yepher/eta-2824-2-watch/output/EXPORTS-2026-09-07.md

# Exports — 2026-09-07

Generated from `watch.cade --part watch` at revision *automatic framework
rebuilt as a stepped stack* (`ERRORS.md` E20, E21).

**The model has grown since the tables in `README.md` were measured**: it is now
**83 part definitions placed 103 times**, against the 71 and 94 those tables
were taken on. Nothing above is withdrawn — it was true of that revision — but
two of its conclusions do not survive the change, and both are re-measured
below. *A measurement has a date on it.*

| file | what it is | size |
|---|---|---|
| `watch.3mf` | the whole assembly, meshed | 141 MB |
| `watch.html` | one self-contained interactive page | 54 MB |
| `watch-raymarch.html` | the same 103 placements, no mesh | 1.6 MB |
| `watch_assembly.step` | **one file**: 43 parts, 54 placements, product tree | 2.2 MB |
| `step/` | the same parts one file each, **43** of them | 2.3 MB |

## Before committing any of this

`watch.3mf` is **141 MB and GitHub rejects a file over 100 MB** — not a warning,
a refused push. `watch.html` at 54 MB is over the 50 MB warning threshold but
goes through. The two options for the 3MF are Git LFS or a Release attachment,
and `README.md` above already recommends the second. The other three files are
small enough to commit normally.

## 3MF

`cade build watch.cade -o watch.3mf --part watch` — **no cell flag**, which is
the change from the README's recipe.

**`--cell 0.095mm` no longer passes.** Re-run today it fails on
`eta_pos_11_third_wheel_envelope` (2 pinched edges), and on the way there
`seconds_hand_envelope` meshes to **0 triangles** — the hands are finer than
that cell. Two more were tried, and the refusals name different parts each time:

| setting | what refuses |
|---|---|
| `--cell 0.1mm` | `eta_pos_16_barrel_bridge_envelope`, 68 pinched edges |
| `--cell 0.15mm` | `seconds_hand_envelope`, **0 triangles** |
| `--cell 0.095mm` | `eta_pos_11_third_wheel_envelope`, 2 pinched edges |
| `-n 64`, `-n 96`, `--cell 0.3mm` | `eta_pos_4_winding_stem_envelope`, 2 closed shells |

So the cell-size search the README describes has run out of answers on this
revision, and the reason is structural rather than bad luck: **the model spans
0.04 mm (hairspring wire) to 32 mm (case), and no single cell holds both.** The
default — each definition meshed on its own grid — is what per-definition grids
exist for, and it is the only setting that writes a valid file here.

**16 763 598 triangles, 8 381 766 vertices, 83 objects, 103 build items**, read
back and confirmed by **lib3mf 2.5.0**, the 3MF Consortium's own reader, which
agrees with cade on every one of those numbers. 1.32 GB as cade writes it
(entries stored); the file here is that archive deflated, which is the README's
own recipe and is legal 3MF — lib3mf and `trimesh` both return identical
geometry from it.

## STEP

`cade export --part watch` still refuses, and now names **41 of 83**:

| definition | faces with no confirmed loop set (n = 128) |
|---|---|
| `eta_pos_10_centre_seconds_wheel_envelope` | 322 of 325 |
| `eta_pos_25_automatic_framework_envelope` | 270 of 287 |
| `eta_pos_12_second_wheel_envelope` | 228 of 231 |
| `eta_pos_19_crown_wheel_envelope` | 158 of 188 |
| `eta_pos_14_barrel_envelope` | 151 of 159 |

No subassembly closes either — `case_and_hands_preview` refuses 6 of 9,
`main_plate_preview` 2 of 5. `step/` holds the **43** that do write. Forty write at `-n 128`; three needed a
raised division count, which is the README's own finding reproducing on a
different revision — and one of the three is the same part it names:

| part | needs |
|---|---|
| `hour_hand_envelope` | `-n 192` — **the README's number, independently** |
| `eta_pos_30_automatic_lower_bridge_envelope` | `-n 192` |
| `eta_pos_14_barrel_envelope` | `-n 256` |

Ten more were swept at 192 and 256 and recovered nothing, so the remaining 38
refuse on their own geometry rather than on resolution, exactly as the README
says of its own 30. `tools/build_step_assembly.py` composes them into
one placed AP214 file exactly as `README.md` describes.

### One file: `watch_assembly.step`

Written by **cade's own assembly writer**, not by an external composer — 43
definitions placed 54 times, with the AP214 product tree, the part names and the
colours, 2.2 MB, at `-n 256`.

The way round the whole-or-nothing rule is not to weaken it. That rule is about
a file that *silently* drops parts, and what it forbids is worth keeping. So
`../watch_exact.cade` is a generated Cade source that **states** which
definitions it contains and where each one sits — every placement is the world
frame `tools/cadeval.py` flattens out of the model — and what cade writes from
it is a *complete* export of a stated selection rather than a truncated export
of the watch. The file lists the 45 definitions left out, by name, in its own
header. Regenerate it with `tools/make_step_assembly.py`; the selection is read
from `step/`, so the two artefacts cannot disagree about what exports.

**Gate.** `cade export`'s own check re-imports the file and runs `verify`, and
it is structurally blind to the product tree, because
`NEXT_ASSEMBLY_USAGE_OCCURRENCE` appears nowhere in cade's importer — a file
whose placements were all wrong would pass it. Read back with **OpenCASCADE
7.9** (`tools/occt-assembly.py` in the cade tree): **54 occurrences, 43 of 43
solids valid, 0 invalid**, each at its located bounding box — the four train
jewels on their own pivots, the crystal at z −2.5 to −1.5, the crown at x 20,
the barrel at 99.995 mm³.

**Why `-n 256` and not the default.** An assembly export runs one `-n` for every
definition in it, and three of the 43 need a raised count of their own — the
barrel (256), the automatic lower bridge and the hour hand (192). At `-n 128`
the file writes in 45 seconds with 40 parts and those three refused; at 256 it
takes about eight minutes and takes all 43. The refusal names them either way,
so there is no silent version of this choice.

### A faceted whole-assembly STEP is now possible and is still not the answer

`cade export --part <assembly> --faceted` was **accepted and silently ignored**
until today — `export` matched the assembly branch before it looked at the flag
— and that is fixed upstream, with a test that fails against the old behaviour.
It does not rescue this model. A faceted `ADVANCED_FACE` costs **503 bytes per
triangle**, measured, so 16.8 M of them is **8.4 GB**, against 141 MB for the
same triangles as a deflated 3MF; and every coarser grid that would shrink it
breaks a part, per the table above. For a mesh of the whole watch, the 3MF is
the format.

## Interactive

- **`watch.html`** — drag to orbit, wheel to zoom, shift-drag to pan, the cube
  snaps to an axis, **hover a row to light that part, click to hide it**, and a
  slider explodes the assembly. Hide the case, caseback and crystal and the
  movement is underneath. Meshed at `-n 48`; `-n 64` and `-n 128` are the same
  command and give 95 MB and 381 MB.
- **`watch-raymarch.html`** — 1.6 MB for the same 103 placements, because the
  page raymarches cade's field per pixel rather than carrying a mesh. Needs
  WebGPU. It has **not** been confirmed rendering: the container it was built in
  loses the WebGPU device on a shader that size, which is a fact about that
  software rasteriser and not about the page, but unverified is unverified.

## Reproducing

```sh
cade build  watch.cade -o watch.3mf  --part watch
cade view   watch.cade -o watch.html --part watch -n 48
cade view   watch.cade -o watch-raymarch.html --part watch --raymarch
cade export eta_2824_design/<module>.cade -o step/<part>.step --part <part> -n 128
```
