yepher/eta-2824-2-watch/rendered/dial.png

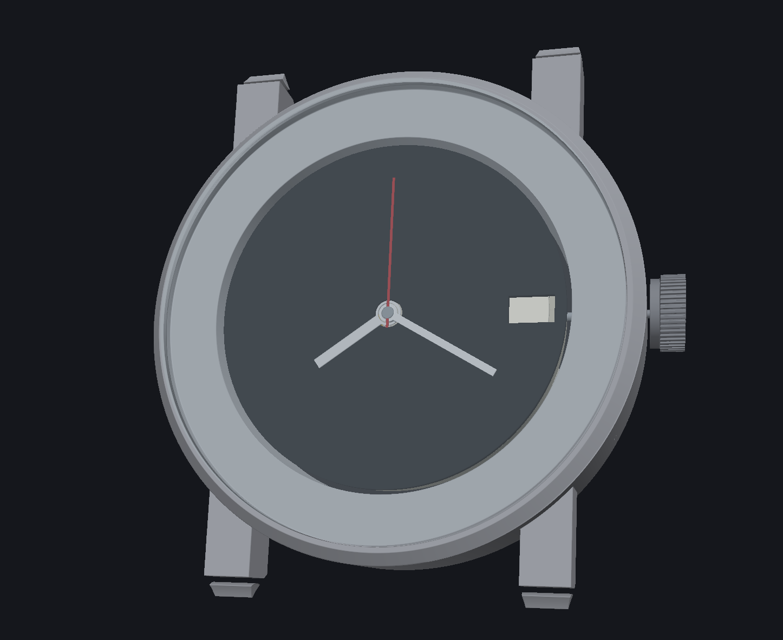
rendered/dial.png
