yepher/eta-2824-2-watch/rendered/exploded_view_editor.png

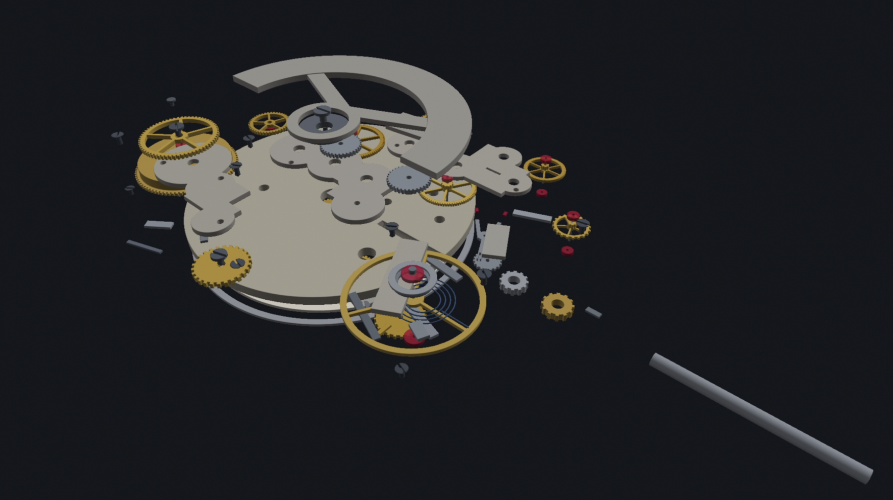
rendered/exploded_view_editor.png
