yepher/eta-2824-2-watch/rendered/thumbs/watch_render_hero.jpg

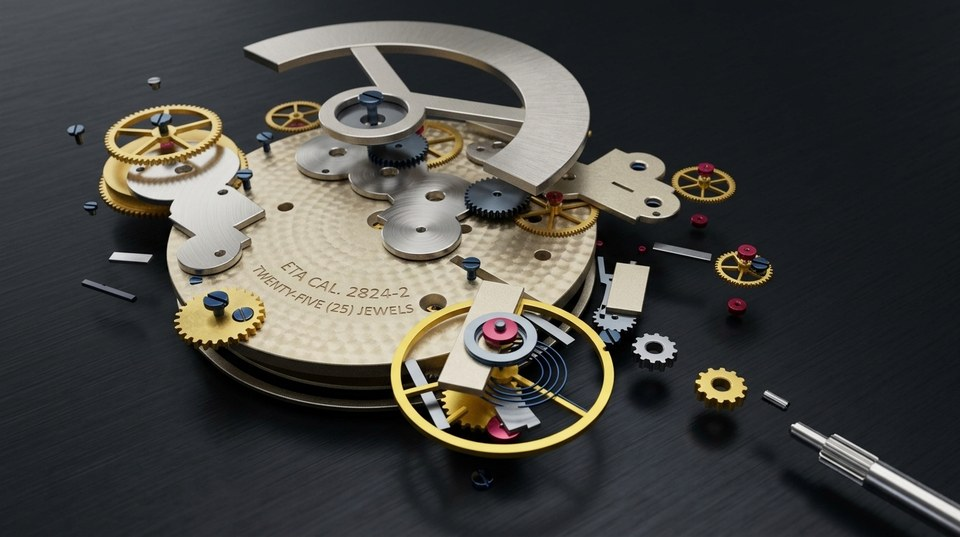
rendered/thumbs/watch_render_hero.jpg
