yepher/eta-2824-2-watch/output/step/eta_pos_7_yoke_envelope.step

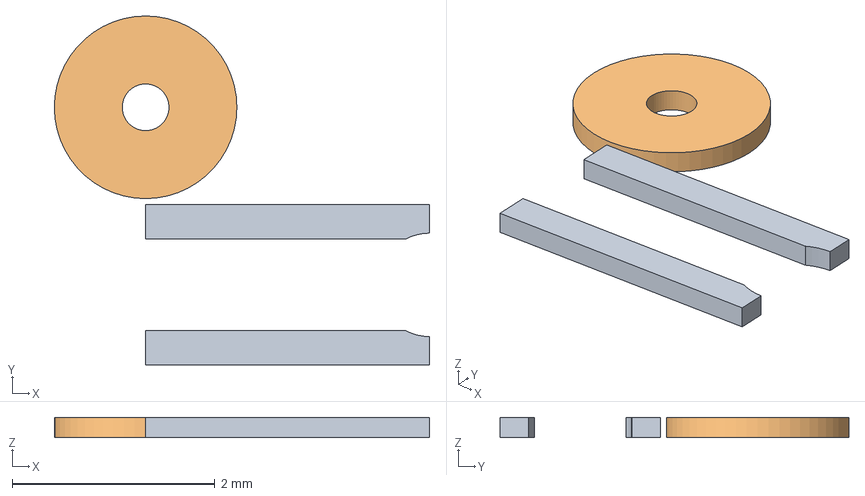
[picture p30: CAD file, 2026-09-07]
output/step/eta_pos_7_yoke_envelope.step
3.70 x 3.44 x 0.2 mm
