yepher/eta-2824-2-watch/output/step/eta_pos_31_3_rotor_pinion.step

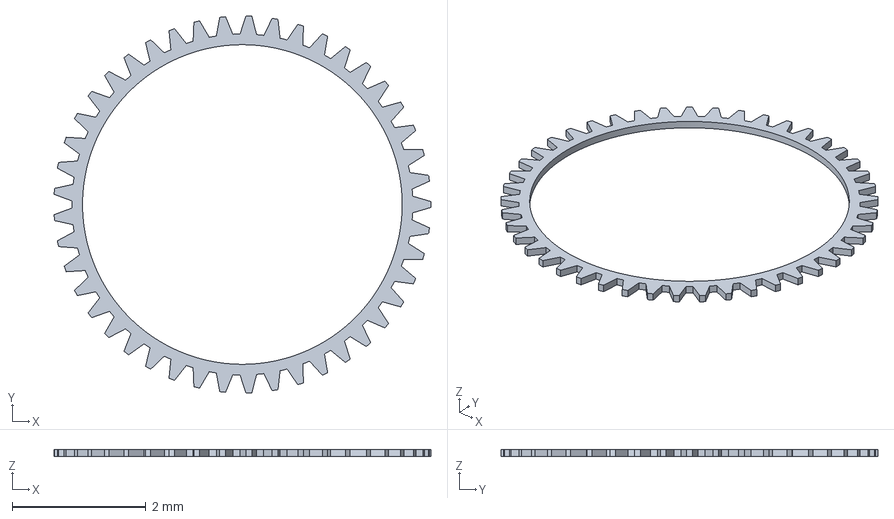
[picture p31: CAD file, 2026-09-07]
output/step/eta_pos_31_3_rotor_pinion.step
5.64 x 5.64 x 0.11 mm
