yepher/eta-2824-2-watch/output/step/eta_pos_23_impulse_jewel.step

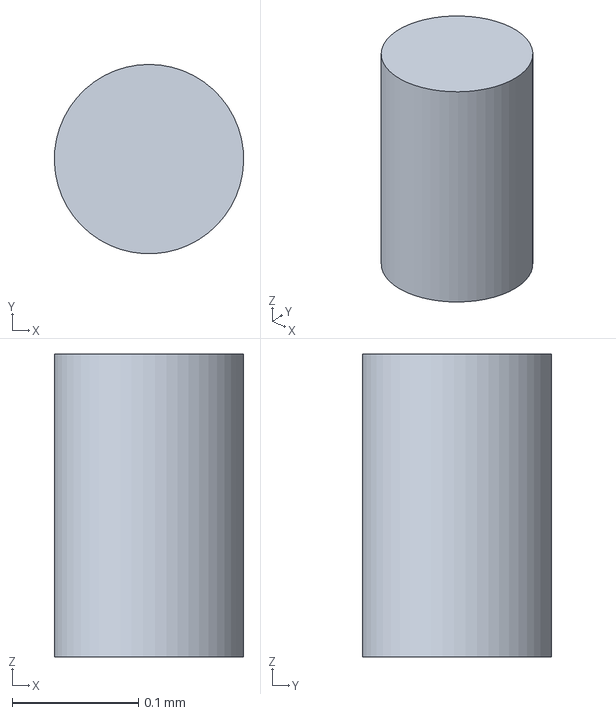
[picture p32: CAD file, 2026-09-07]
output/step/eta_pos_23_impulse_jewel.step
0.15 x 0.15 x 0.24 mm
