yepher/eta-2824-2-watch/output/step/eta_pos_23_balance_staff.step

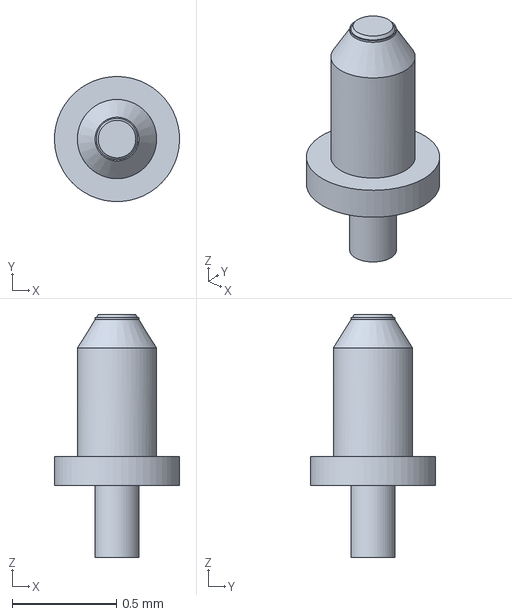
[picture p33: CAD file, 2026-09-07]
output/step/eta_pos_23_balance_staff.step
0.6 x 0.599 x 1.17 mm
