yepher/eta-2824-2-watch/output/step/eta_pos_6_setting_lever_envelope.step

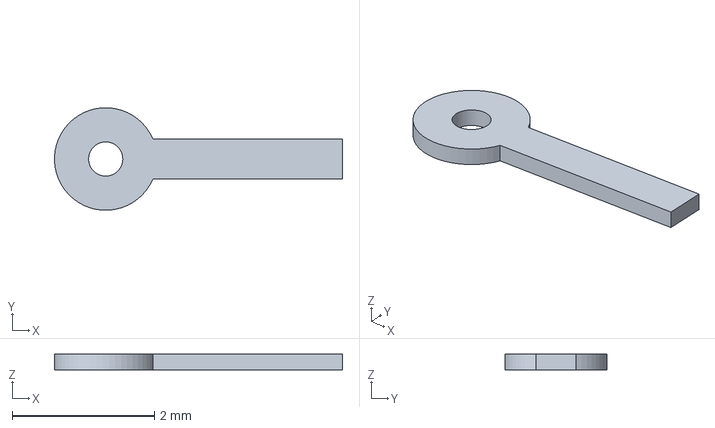
[picture p34: CAD file, 2026-09-07]
output/step/eta_pos_6_setting_lever_envelope.step
4.04 x 1.44 x 0.22 mm
