yepher/eta-2824-2-watch/output/step/click_post.step

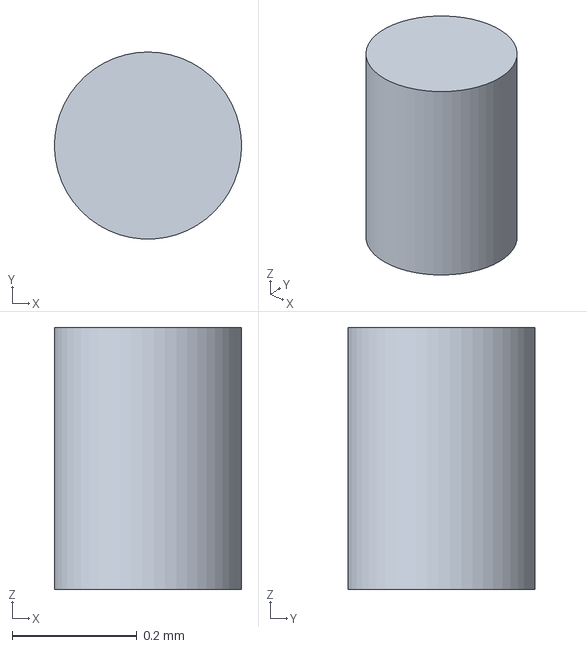
[picture p35: CAD file, 2026-09-07]
output/step/click_post.step
0.3 x 0.3 x 0.42 mm
