yepher/eta-2824-2-watch/output/step/eta_pos_33_cannon_pinion_envelope.step

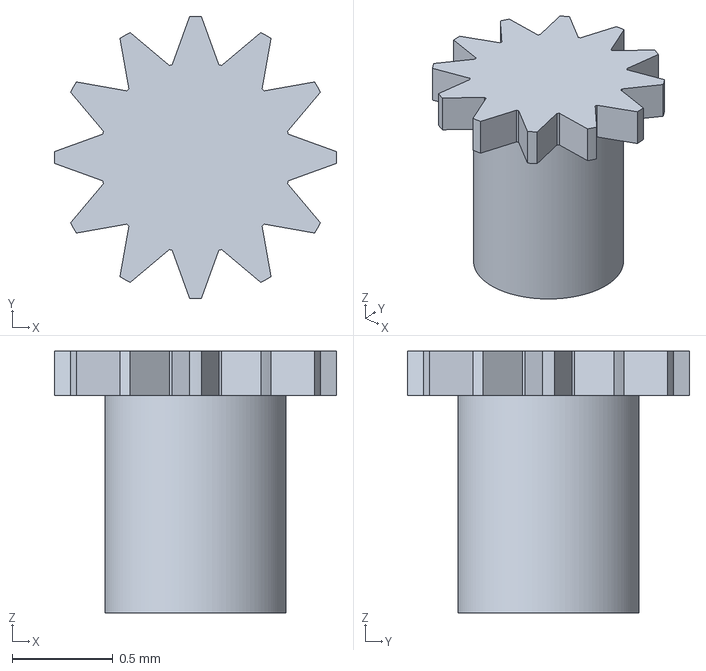
[picture p36: CAD file, 2026-09-07]
output/step/eta_pos_33_cannon_pinion_envelope.step
1.40 x 1.40 x 1.30 mm
