yepher/eta-2824-2-watch/output/step/eta_pos_14_barrel_envelope.step

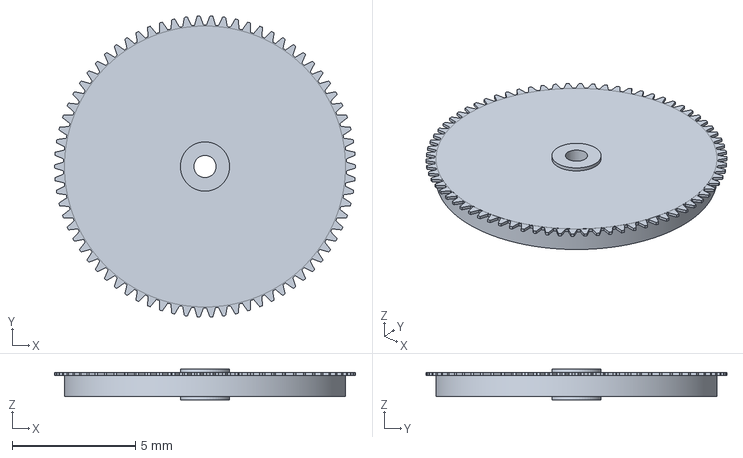
[picture p37: CAD file, 2026-09-07]
output/step/eta_pos_14_barrel_envelope.step
12.2 x 12.2 x 1.25 mm
