yepher/eta-2824-2-watch/output/step/eta_pos_17_click_envelope.step

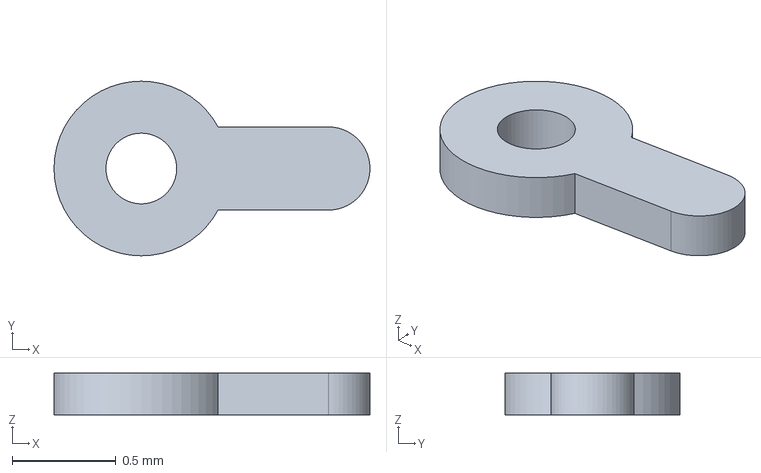
[picture p38: CAD file, 2026-09-07]
output/step/eta_pos_17_click_envelope.step
1.52 x 0.84 x 0.2 mm
