yepher/eta-2824-2-watch/output/step/eta_pos_13_train_bridge_jewel.step

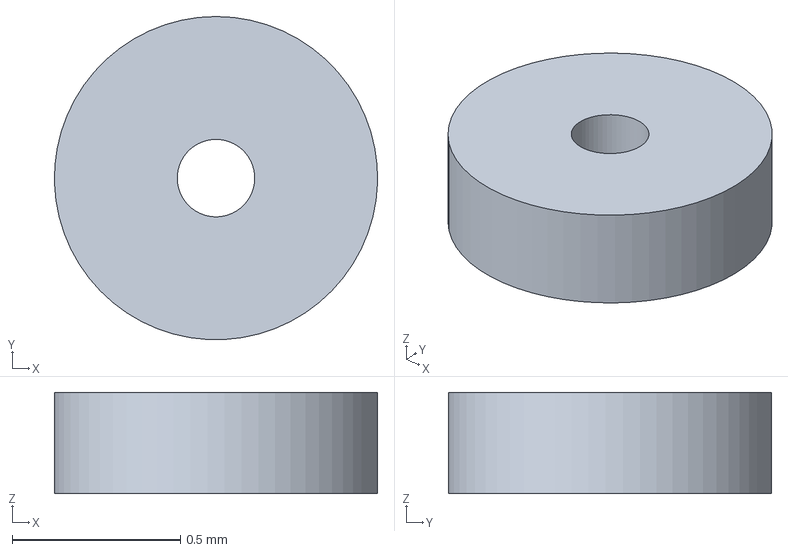
[picture p39: CAD file, 2026-09-07]
output/step/eta_pos_13_train_bridge_jewel.step
0.96 x 0.959 x 0.3 mm
