yepher/eta-2824-2-watch/output/step/going_train_pivot_arbor.step

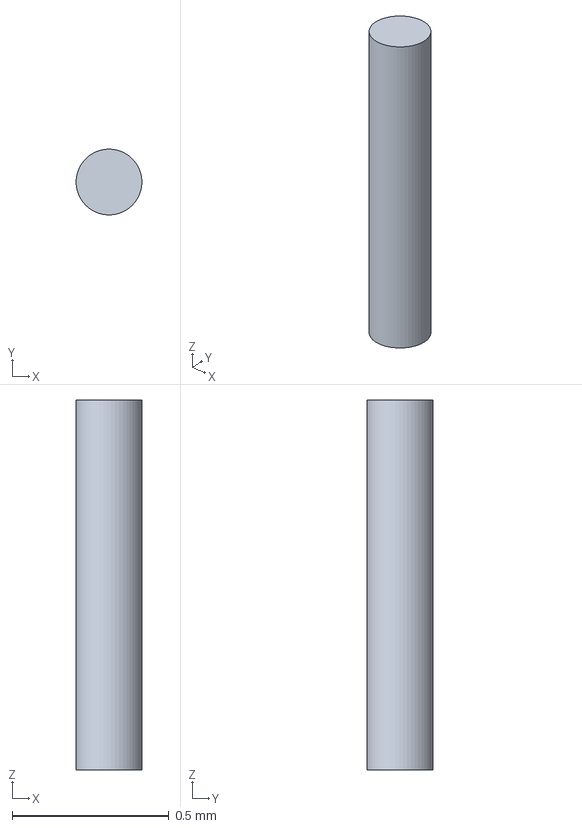
[picture p40: CAD file, 2026-09-07]
output/step/going_train_pivot_arbor.step
0.21 x 0.21 x 1.18 mm
