yepher/eta-2824-2-watch/output/step/eta_pos_31_2_ball_bearing_envelope.step

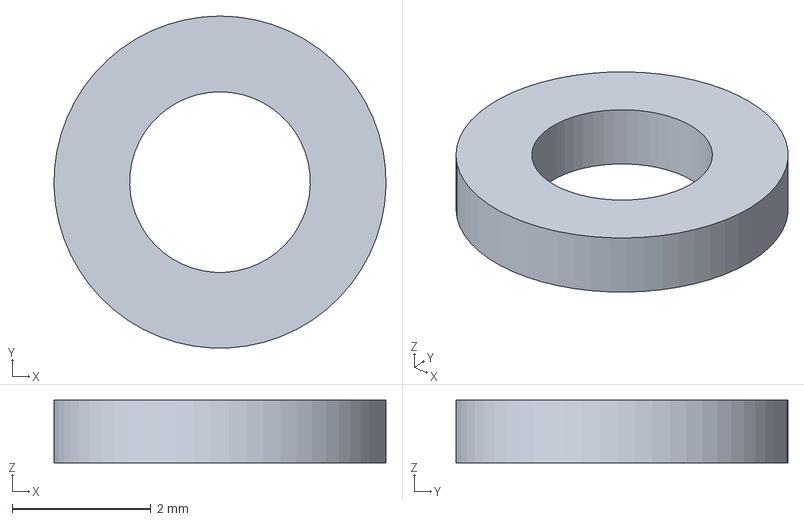
[picture p41: CAD file, 2026-09-07]
output/step/eta_pos_31_2_ball_bearing_envelope.step
4.78 x 4.78 x 0.9 mm
