yepher/eta-2824-2-watch/output/step/eta_pos_30_automatic_lower_bridge_envelope.step

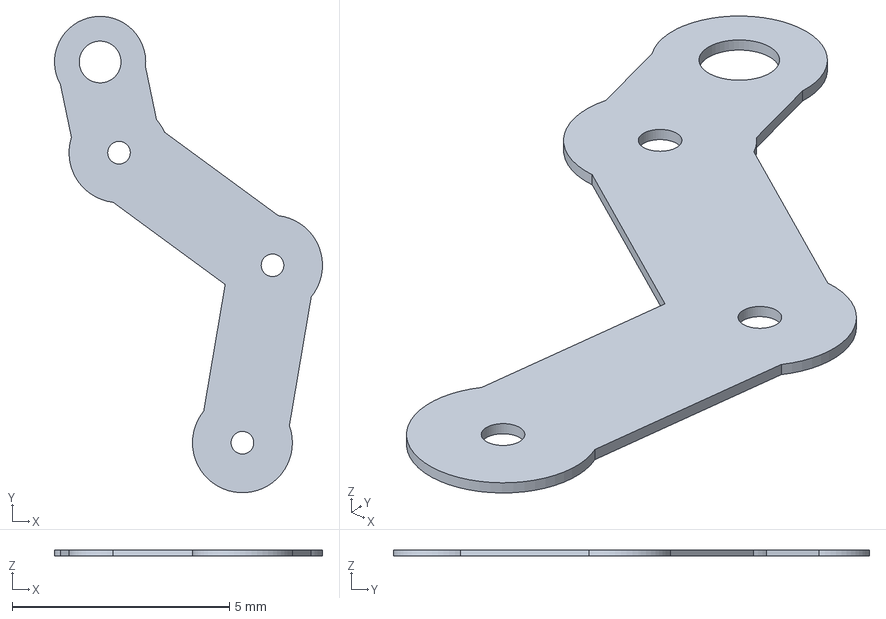
[picture p42: CAD file, 2026-09-07]
output/step/eta_pos_30_automatic_lower_bridge_envelope.step
6.17 x 11.0 x 0.14 mm
