yepher/eta-2824-2-watch/output/step/eta_pos_32_setting_wheel_envelope.step

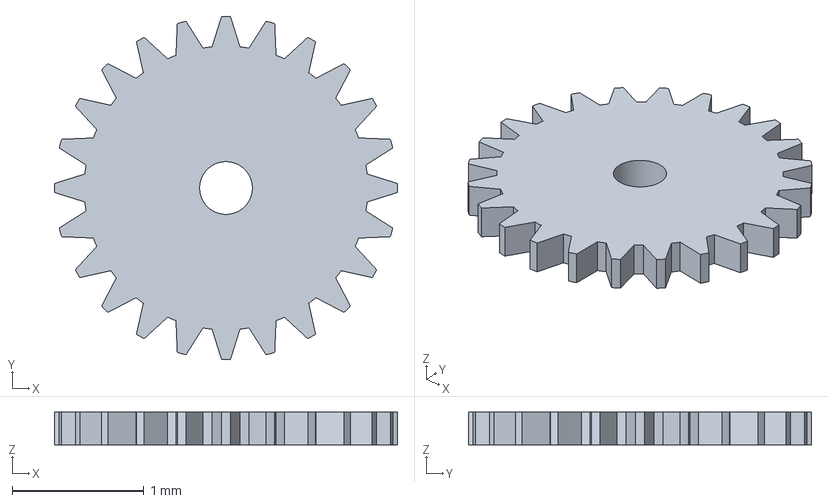
[picture p43: CAD file, 2026-09-07]
output/step/eta_pos_32_setting_wheel_envelope.step
2.60 x 2.60 x 0.25 mm
