yepher/eta-2824-2-watch/output/step/crown_envelope.step

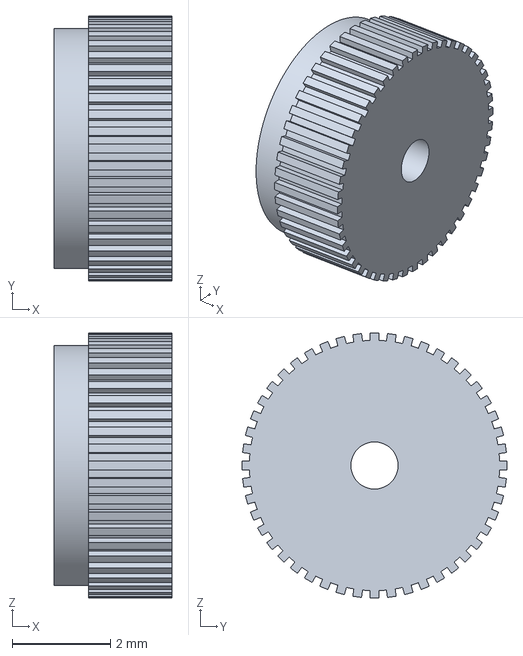
[picture p44: CAD file, 2026-09-07]
output/step/crown_envelope.step
2.40 x 5.40 x 5.40 mm
