yepher/eta-2824-2-watch/output/step/eta_pos_5_corrector_lever_envelope.step

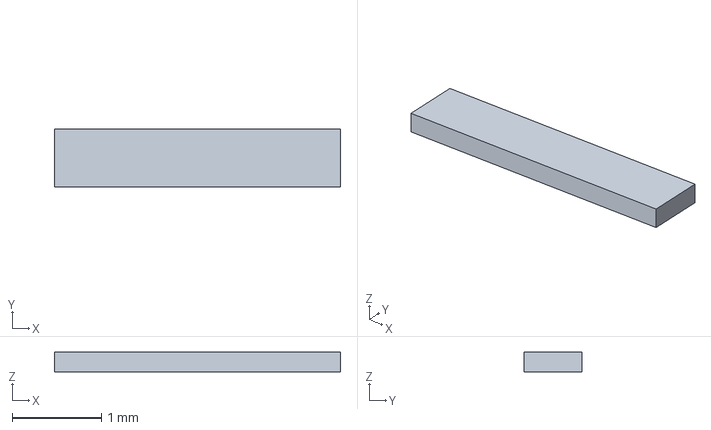
[picture p45: CAD file, 2026-09-05]
output/step/eta_pos_5_corrector_lever_envelope.step
3.20 x 0.65 x 0.22 mm
