yepher/eta-2824-2-watch/output/step/eta_pos_24_4_upper_index_envelope.step

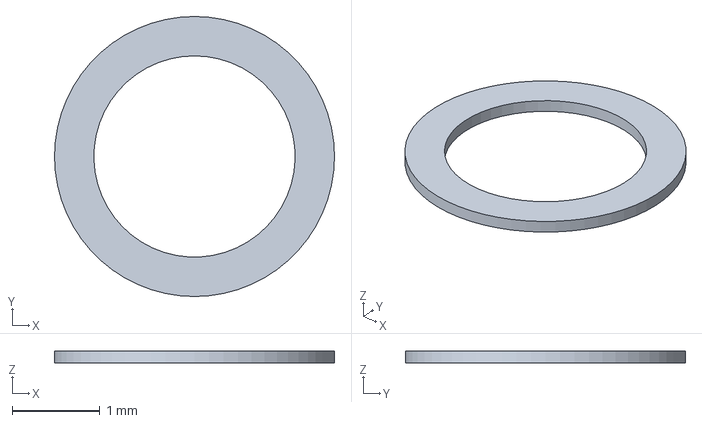
[picture p46: CAD file, 2026-09-05]
output/step/eta_pos_24_4_upper_index_envelope.step
3.20 x 3.20 x 0.14 mm
