yepher/eta-2824-2-watch/output/step/eta_pos_24_5_regulator_corrector_envelope.step

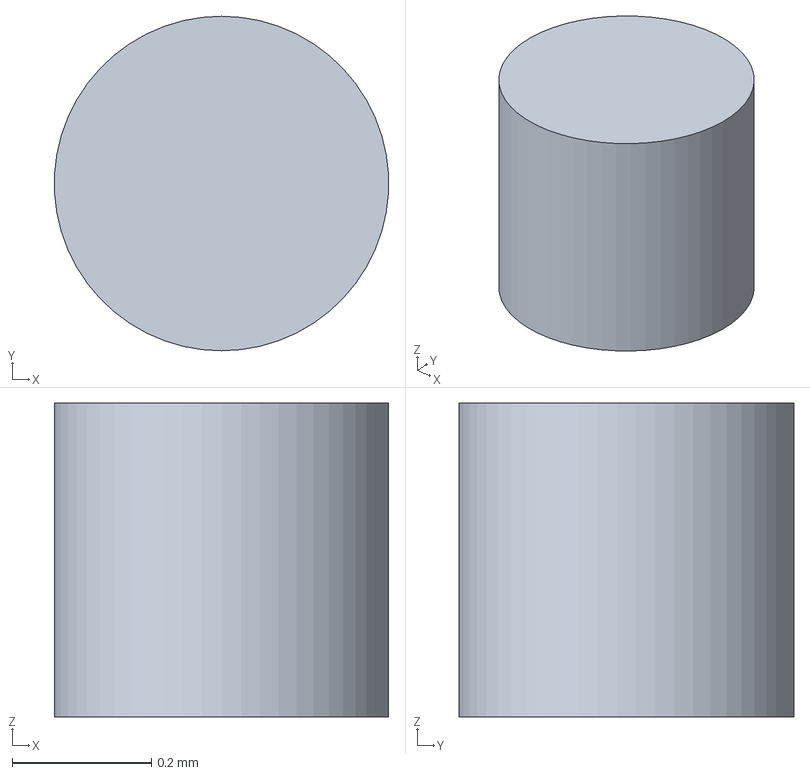
[picture p47: CAD file, 2026-09-05]
output/step/eta_pos_24_5_regulator_corrector_envelope.step
0.479 x 0.48 x 0.45 mm
