yepher/eta-2824-2-watch/output/step/eta_pos_1_barrel_plate_jewel.step

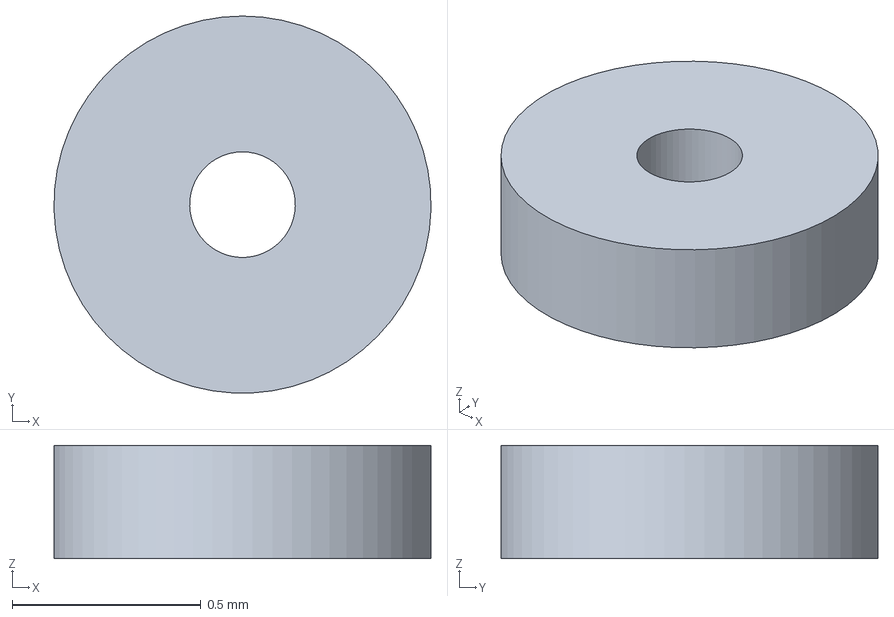
[picture p48: CAD file, 2026-09-05]
output/step/eta_pos_1_barrel_plate_jewel.step
1 x 0.999 x 0.3 mm
