yepher/eta-2824-2-watch/output/step/eta_pos_42_dial_support_envelope.step

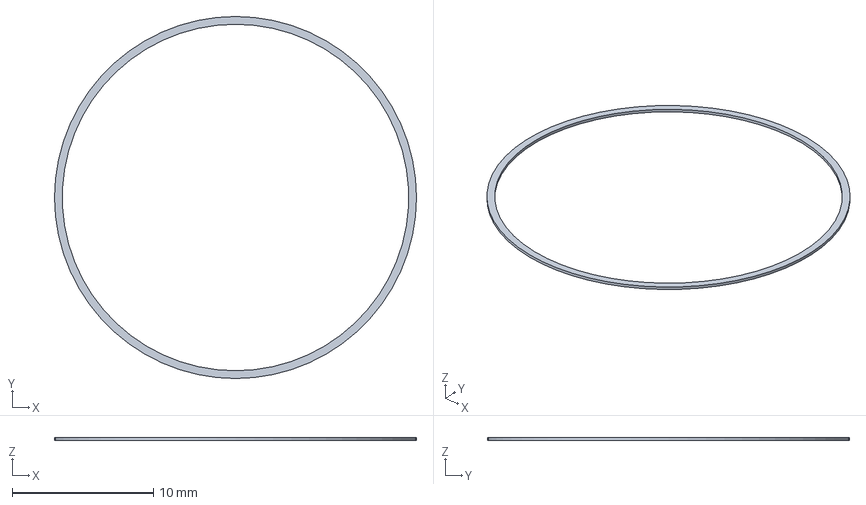
[picture p49: CAD file, 2026-09-05]
output/step/eta_pos_42_dial_support_envelope.step
25.6 x 25.6 x 0.2 mm
