yepher/eta-2824-2-watch/output/step/eta_pos_1_2_lower_shock_absorber_envelope.step

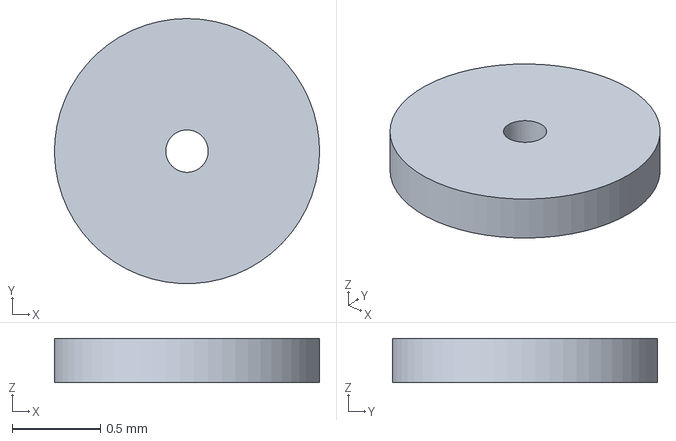
[picture p50: CAD file, 2026-09-05]
output/step/eta_pos_1_2_lower_shock_absorber_envelope.step
1.50 x 1.50 x 0.25 mm
