yepher/eta-2824-2-watch/output/step/eta_pos_24_3_lower_index_envelope.step

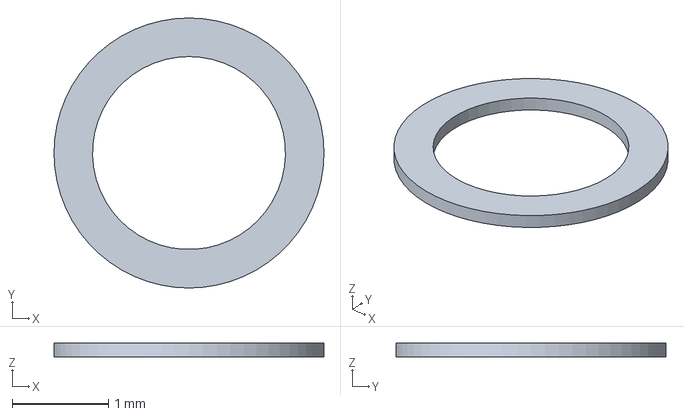
[picture p51: CAD file, 2026-09-05]
output/step/eta_pos_24_3_lower_index_envelope.step
2.80 x 2.80 x 0.14 mm
