yepher/eta-2824-2-watch/output/step/eta_pos_15_stop_lever_envelope.step

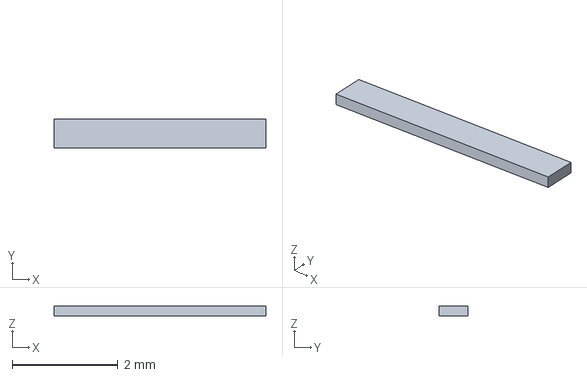
[picture p52: CAD file, 2026-09-05]
output/step/eta_pos_15_stop_lever_envelope.step
4.00 x 0.55 x 0.18 mm
