yepher/eta-2824-2-watch/output/step/eta_pos_24_2_stud_support_envelope.step

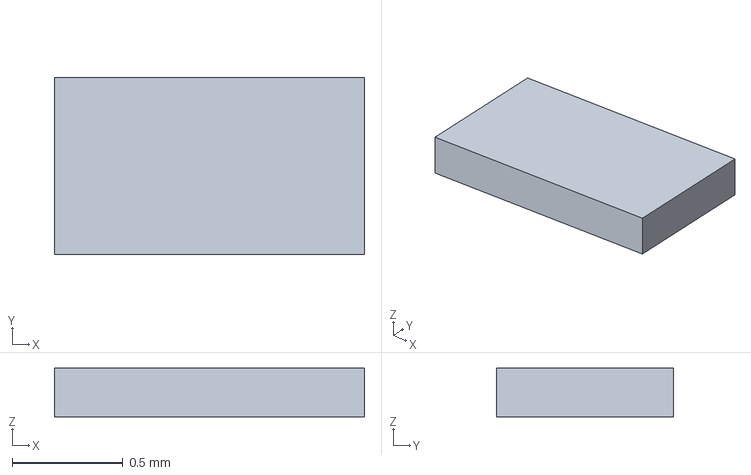
[picture p53: CAD file, 2026-09-05]
output/step/eta_pos_24_2_stud_support_envelope.step
1.40 x 0.8 x 0.22 mm
