yepher/eta-2824-2-watch/output/step/eta_pos_8_setting_lever_jumper_envelope.step

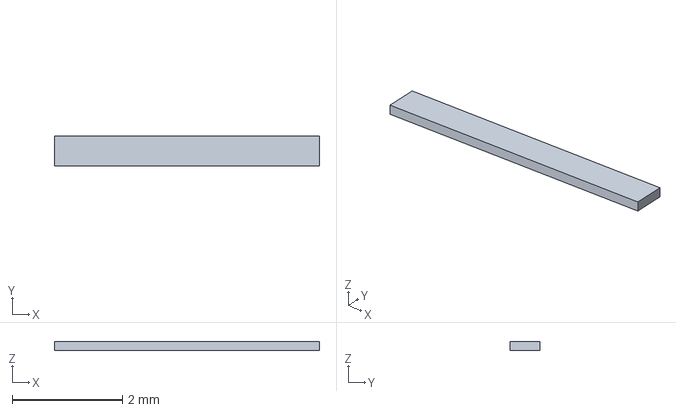
[picture p54: CAD file, 2026-09-05]
output/step/eta_pos_8_setting_lever_jumper_envelope.step
4.80 x 0.55 x 0.16 mm
