yepher/eta-2824-2-watch/output/step/hour_hand_envelope.step

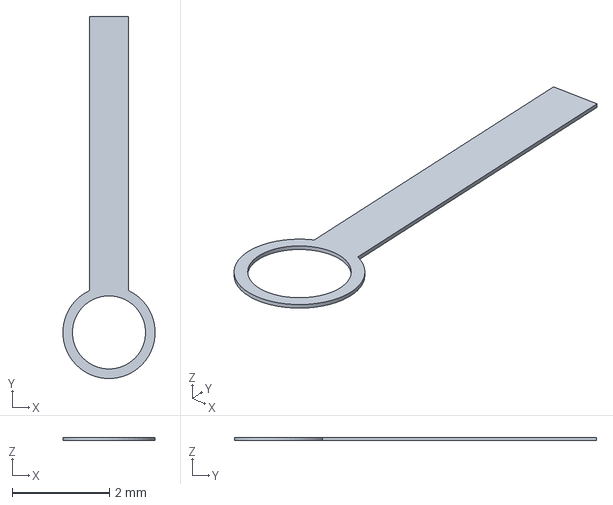
[picture p55: CAD file, 2026-09-05]
output/step/hour_hand_envelope.step
1.90 x 7.45 x 0.06 mm
