yepher/eta-2824-2-watch/output/step/dial_envelope.step

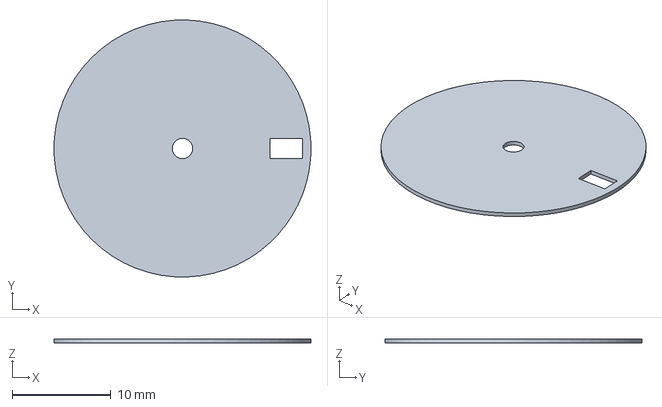
[picture p56: CAD file, 2026-09-05]
output/step/dial_envelope.step
26.0 x 26.0 x 0.4 mm
