yepher/eta-2824-2-watch/output/step/eta_pos_40_date_jumper_envelope.step

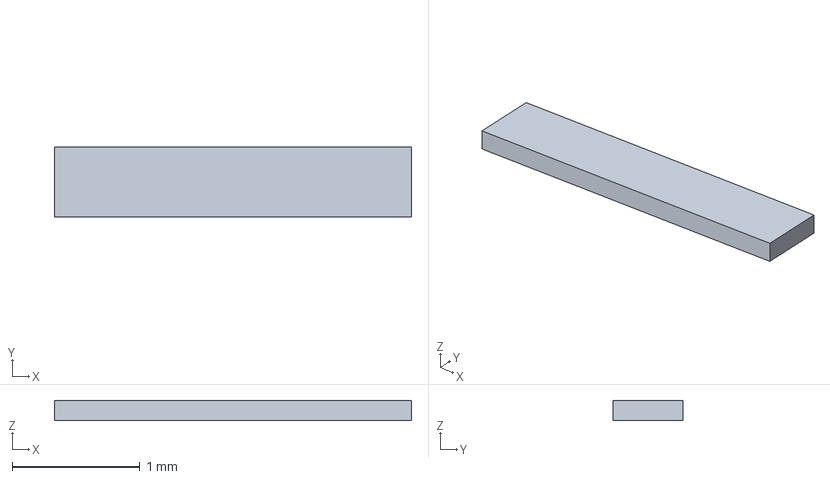
[picture p57: CAD file, 2026-09-05]
output/step/eta_pos_40_date_jumper_envelope.step
2.80 x 0.55 x 0.16 mm
